skykraft-au/Turtle-GPS-orbit-determination-system/GPS v2.0/Software and HDL/Verilog Project/GPS_V2.0/GPS_V2.0.gen/sources_1/ip/DDS_Gen/hdl/dds_compiler_v6_0_core.vhd

`protect begin_protected
`protect version = 1
`protect encrypt_agent = "XILINX"
`protect encrypt_agent_info = "Xilinx Encryption Tool 2024.1"
`protect key_keyowner = "Synopsys", key_keyname = "SNPS-VCS-RSA-2", key_method = "rsa"
`protect encoding = (enctype = "BASE64", line_length = 76, bytes = 128)
`protect key_block
QwzFJmGcmuiKddE+BYFoDvgdr5RCDU8RbXMXhOK+y3PeocMYwGQprU06gy6+uULddPdY1d7Zpkl4
8PLD9UUy/XTRIMRkKFF8iGwcy4GukjF+wF//IfzFlL7UzfIynEfTE9BZnkKrGSgEtvrrieEPogs6
4cHoUeICIlYn2vaCq1U=

`protect key_keyowner = "Aldec", key_keyname = "ALDEC15_001", key_method = "rsa"
`protect encoding = (enctype = "BASE64", line_length = 76, bytes = 256)
`protect key_block
A5TDtolvoT8jrAmuJHkafqS9OHu6Gq/PMmm1EtAJgSJSLKbu8jW7A8ZF3/HKxkKmRmFUILHUKYlR
QfHZS4GmEVtWCEWtKpqBFqWJFaCOU0d7Z52FYUUNsrHsjemkExK3X+d+4zmcvoWkt0PpF6he3x3Z
H2Hfm0DzIC6BxqRq+fbN4r1Y3CxkJWUGWSFGDAUyqrC4lFM3y2zFtsedwywPj9k7ZPBckA4rSeQ+
4xZ9PrIwtQXxLQ95tJQ/FblrFLD/khI7gm+pfS8MzQZX3cTOi3IEaATad8E6H21q4AlXRIjcZ5aZ
fsIQVJKxmoAW+tkpAvvqpKaZSSHZDG7/Zfpxvg==

`protect key_keyowner = "Mentor Graphics Corporation", key_keyname = "MGC-VELOCE-RSA", key_method = "rsa"
`protect encoding = (enctype = "BASE64", line_length = 76, bytes = 128)
`protect key_block
q4nXc6vDv7SCwovcUQ8mg0ddt/6HzaQq5knTykAAhGFX5GDr/On+XnH0gJb/s5YAZ+efacireUfc
0/7oLdu6vx0IlQEdvxciUTh5LeYn/dCh/dofsZIYIkbcmvUS+lYKQbVsMZD08GDHLFFhxLzvKnQY
yO4XzYtKXm/gRIyc1B8=

`protect key_keyowner = "Mentor Graphics Corporation", key_keyname = "MGC-VERIF-SIM-RSA-2", key_method = "rsa"
`protect encoding = (enctype = "BASE64", line_length = 76, bytes = 256)
`protect key_block
Bi4/JvsyXYWliqe8C97RzFYYL+5kiQY48Rw9+WmFLdezOov8H+z/OR8MhkrrzYvN87xpcvNumpgC
XbM/cnArMPPf/kW0xBOJScjqvhW8Ch6eXrqmpDq0wgHJ7ahHoEKvI2I3h9/8W6URIi9LnpW+EG04
V+nqTAlVPRJu9twstL3wERy1kw7PdVYH26vnZfSDji5/Ck6Dj12abH5szgZRd1vF5511xHPwUxOx
zJUa1megV9zt0UR/jy2bq5rBQBoP3t5I1YhjCZZBtJB0pRaoJr3u674oG32/sIJiuIGfr5YQ1OYW
NqS9gt+0Mar/sFqAnXnlQzog3HA7Y30pcndu7Q==

`protect key_keyowner = "Real Intent", key_keyname = "RI-RSA-KEY-1", key_method = "rsa"
`protect encoding = (enctype = "BASE64", line_length = 76, bytes = 256)
`protect key_block
ItL89heSfN5sCFq5IhssGXFB+J/tRcmaKBFe7SV8TL+P9IJPXrY3zAmA6bnheHyj8UMWnpVL+8WZ
MtjLIYzaKoFjtqxeor5r62jajXcS7MZ5rQBuE//VX4MT/FmGvm70+pUPvoGjqy/7l9v0I0hZa+W8
WR/atwdtQRRqQDm8BkCsQbdz5dsyzGemnbBgY2/50td0bx56mHVO3ibR6YVaff5XSo7X6GaOjYZc
uav2Y7SZwIaMGqT4HTDKngEcU/EbMAPa8omcjSNT78MK28l4k1c2Nj/bRIlHNQgEb/6IXnP/2X0P
9KqaEIO1exETmm7qd0yUKPDoVjcPmYdcIqh4dQ==

`protect key_keyowner = "Xilinx", key_keyname = "xilinxt_2023_11", key_method = "rsa"
`protect encoding = (enctype = "BASE64", line_length = 76, bytes = 256)
`protect key_block
s/MMLYeEJjrvFPxblPwSTTZm363UgI35H03Nc3Qjmxxt0s/ujUUeYyBel64pJMZGDJKPX/i5sx6Z
cdtOD3cpHdZdZXPuMdZ4qfSzthwl7nBseISCQ4FaK2qxVVq45u6tDhEsHfZPEPKiSfn9oxmy59MC
cQJClufehfd+YKhkuoF0Qnt9WSa0vWMQmExrZpsudJGrcgiNurIdfd99Wj7Ve62/qN4IpkTT6Bej
wZuDbi74E26J+N9T9ZVC1tZzcKBwceUyWHOreS2l87fLYFlR76sDfyFXB7MRk3TXwkfvXE3r//4L
BKMHceBKA+T0BNXyI3pF/No6ajgPnjZl6C/Beg==

`protect key_keyowner = "Metrics Technologies Inc.", key_keyname = "DSim", key_method = "rsa"
`protect encoding = (enctype = "BASE64", line_length = 76, bytes = 256)
`protect key_block
iU0iiUsqMoLiXYDQyD0xNh0he8Hb+dVzANumn57cZoUJPt5x/SmPwNhA5lLdPYlmMIa5onU3Nvlv
ebtnoxdB/DjX3WUhrLOKHW3w6167rUBrgZtuXuX4JhmP7dbPHm+/afSj4cesQJubVLODCCcxyNca
ZXvNA7647G/g0je3B+SVjUzdnN7/NDjGDEzyVGAfVXCMgODpbdE/jna1bEjJbqi9NQhw5YZH2CAg
iXP5NDDnPA6WHWKe5HnKO1a9QwLtxN936GztodWGx3qx0or93h5iNAUsFq+AVMN08/E8pfjNRlDL
xKWAnxQ7T9pjmQDosH/9IS/VZTgj9fmtfUM7UA==

`protect key_keyowner = "Atrenta", key_keyname = "ATR-SG-RSA-1", key_method = "rsa"
`protect encoding = (enctype = "BASE64", line_length = 76, bytes = 384)
`protect key_block
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

`protect key_keyowner = "Cadence Design Systems.", key_keyname = "CDS_RSA_KEY_VER_1", key_method = "rsa"
`protect encoding = (enctype = "BASE64", line_length = 76, bytes = 256)
`protect key_block
bVfzIBiijAjUMZrGuUCb22zYY2OJET1A1hOtMbpVq8ZnKczRf7Zvybh2sVrWqJZsuG4kK1pu1Ek2
FJfBLqF2VR/0OfAJzJjvI/CsR+YxNAIbBspFhBWHf//cqji7L1NCEoQALr80vXYInRgVAmbaSw4E
4Chcwfy5wouUE0bhR3hd69c7cJjZaADg48C6nFC07pL7O8hxMMMAnu2DfVHgJivO7vbZns6cVmIP
ThJOO5aYXSZLW0f8us5JcrY8ilO0VUpo/rmh6KFGOQDGz0HMXoFVqlzytcb93LVy/viq31gnT9Dk
iHCwM0VStm3BY8iOT0Th5e7IV+OFr/9HWsta2w==

`protect data_method = "AES128-CBC"
`protect encoding = (enctype = "BASE64", line_length = 76, bytes = 59968)
`protect data_block
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
naOwBQ==
`protect end_protected
